MakotoKurauchi/helix/PCB/beta/helix.sch

## KiCad design PCB/beta/helix.sch (2018-01-27)

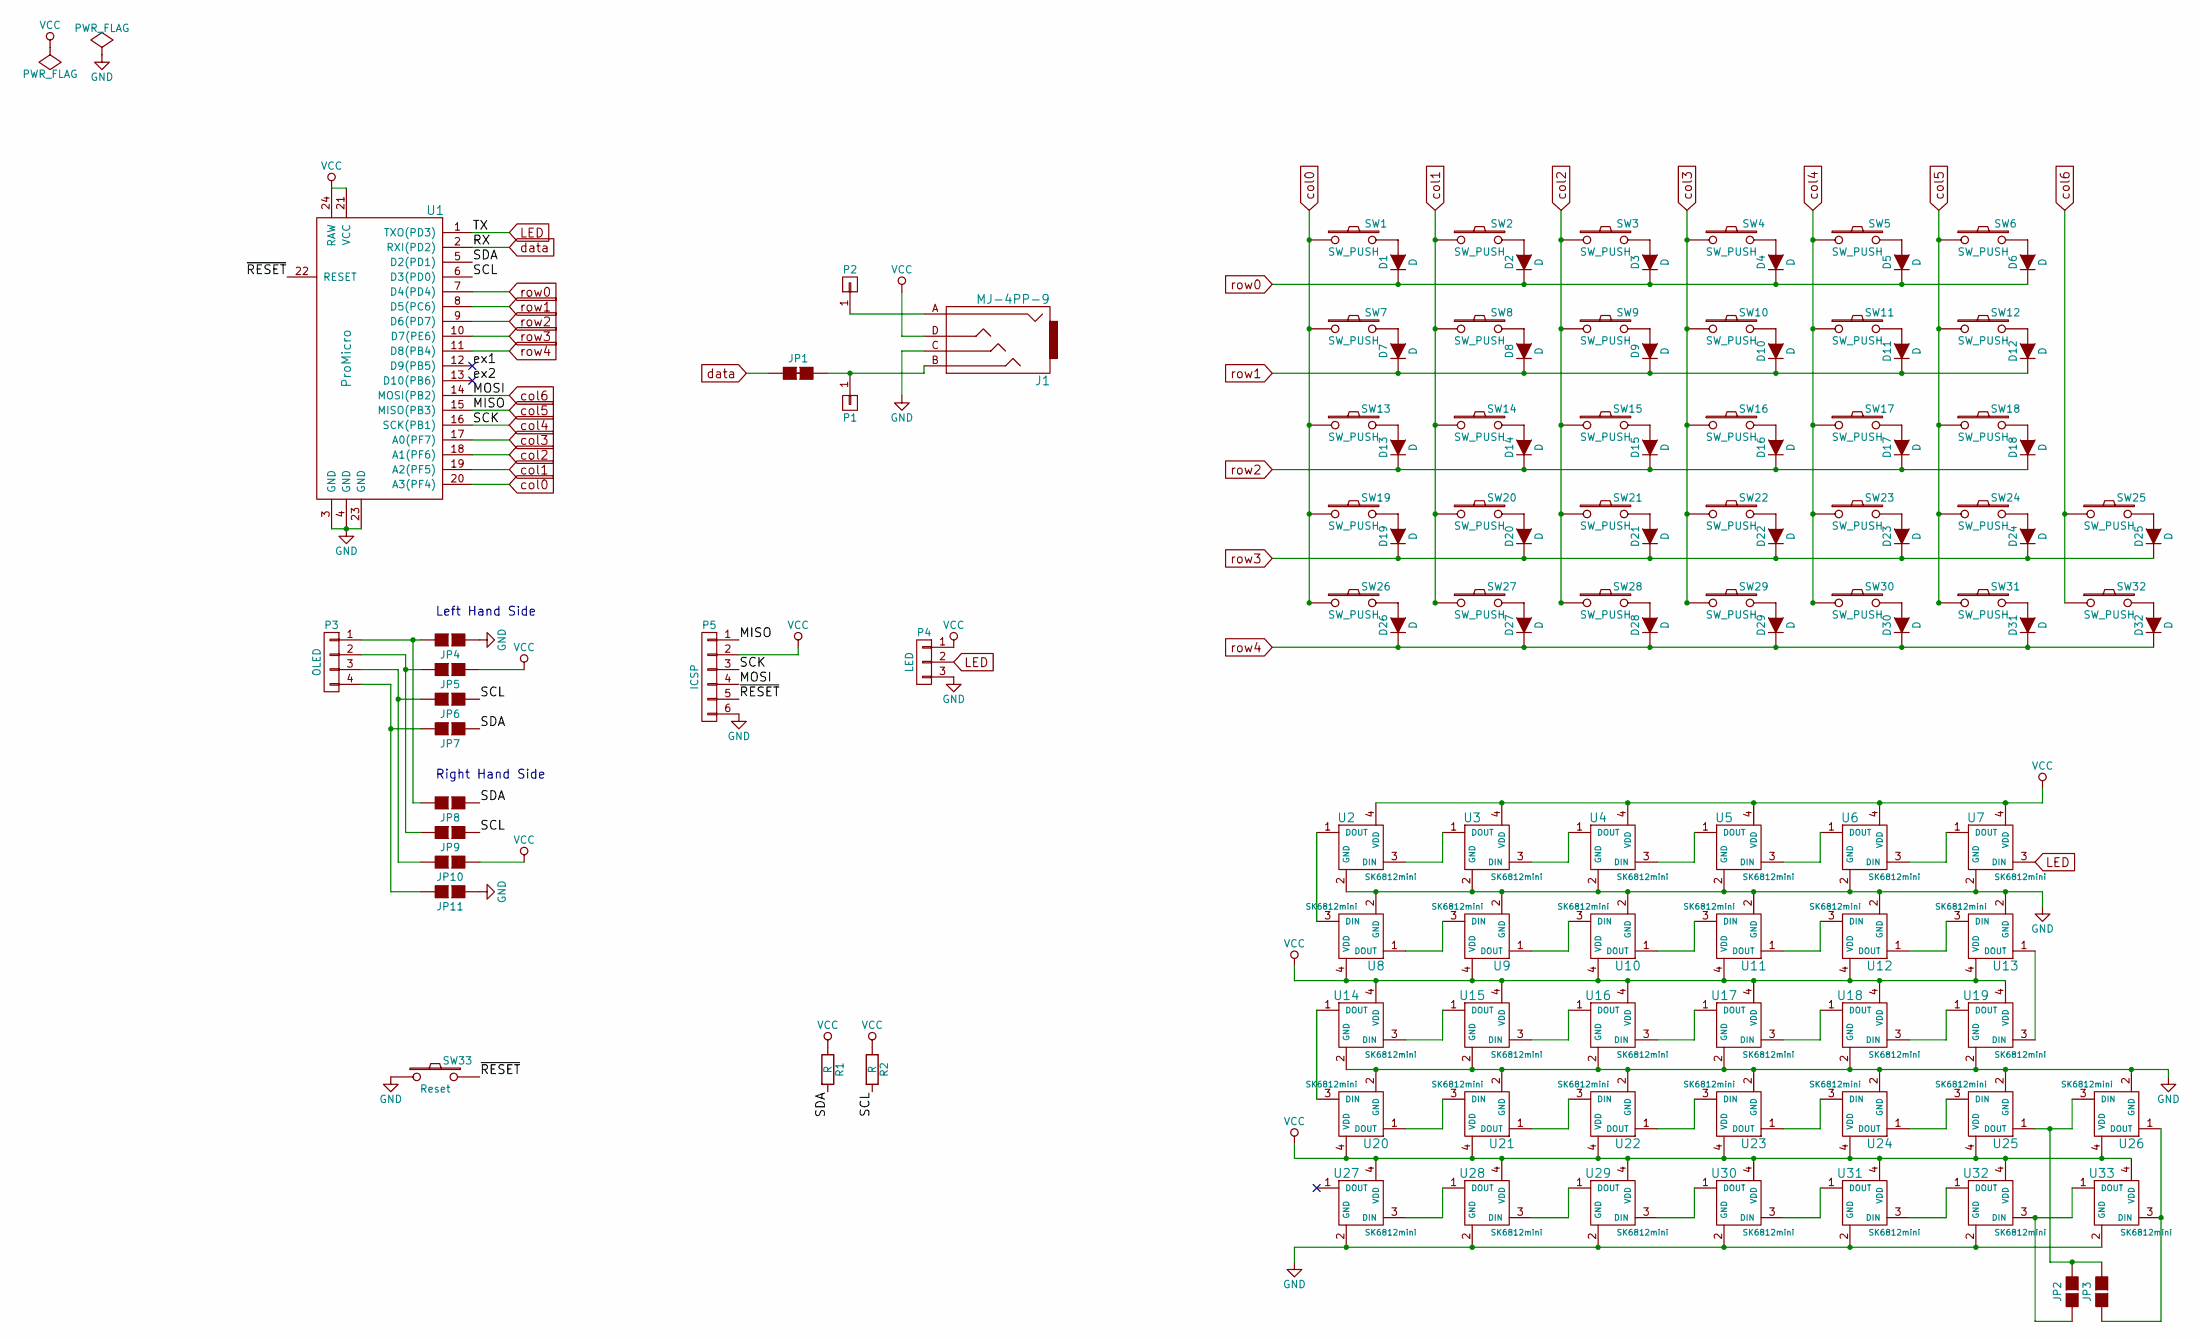
[picture p5: schematic helix.sch]

Parts:
D1, D2, D3, D4, D5, D6, D7, D8, D9, D10, D11, D12, D13, D14, D15, D16, D17, D18, D19, D20, D21, D22, D23, D24, D25, D26, D27, D28, D29, D30, D31, D32: D; D3_TH_SMD
J1: MJ-4PP-9; MJ-4PP-9_rev2
JP1: JPC2
JP2, JP3: JP2; Jumper
JP4, JP11: GND; Jumper
JP5, JP10: VCC; Jumper
JP6, JP9: SCL; Jumper
JP7, JP8: SDA; Jumper
P1, P2: CONN_01X01; 1PIN_0.1
P3: OLED; MY_SIL-4
P4: LED; StripLED_rev
P5: ICSP; MY_SIL-2x3
R1, R2: R; R2
SW1, SW2, SW3, SW4, SW5, SW6, SW7, SW8, SW9, SW10, SW11, SW12, SW13, SW14, SW15, SW16, SW17, SW18, SW19, SW20, SW21, SW22, SW23, SW24, SW25, SW26, SW27, SW28, SW29, SW30, SW31, SW32: SW_PUSH; MX_ALPS_PG1350_noLed
SW33: Reset; SW_3.5x6.0_TH
U1: ProMicro; ProMicro_rev
U2, U3, U4, U5, U6, U7, U8, U9, U10, U11, U12, U13, U14, U15, U16, U17, U18, U19, U20, U21, U22, U23, U24, U25, U26, U27, U28, U29, U30, U31, U32, U33: SK6812mini; SK6812MINI_rev

Connections:
GND: J1.C, JP4.1 (G1), JP11.1 (G1), P4.3, P5.6, SW33.1, U1.3 (GND), U1.4 (GND), U1.23 (GND), U2.2 (GND), U3.2 (GND), U4.2 (GND), U5.2 (GND), U6.2 (GND), U7.2 (GND), U8.2 (GND), U9.2 (GND), U10.2 (GND), U11.2 (GND), U12.2 (GND), U13.2 (GND), U14.2 (GND), U15.2 (GND), U16.2 (GND), U17.2 (GND), U18.2 (GND), U19.2 (GND), U20.2 (GND), U21.2 (GND), U22.2 (GND), U23.2 (GND), U24.2 (GND), U25.2 (GND), U26.2 (GND), U27.2 (GND), U28.2 (GND), U29.2 (GND), U30.2 (GND), U31.2 (GND), U32.2 (GND), U33.2 (GND)
LED: P4.2, U1.1 (TXO(PD3)), U7.3 (DIN)
unnamed: D1.2 (A), SW1.2
unnamed: D2.2 (A), SW2.2
unnamed: D3.2 (A), SW3.2
unnamed: D4.2 (A), SW4.2
unnamed: D5.2 (A), SW5.2
unnamed: D6.2 (A), SW6.2
unnamed: D7.2 (A), SW7.2
unnamed: D8.2 (A), SW8.2
unnamed: D9.2 (A), SW9.2
unnamed: D10.2 (A), SW10.2
unnamed: D11.2 (A), SW11.2
unnamed: D12.2 (A), SW12.2
unnamed: D13.2 (A), SW13.2
unnamed: D14.2 (A), SW14.2
unnamed: D15.2 (A), SW15.2
unnamed: D16.2 (A), SW16.2
unnamed: D17.2 (A), SW17.2
unnamed: D18.2 (A), SW18.2
unnamed: D19.2 (A), SW19.2
unnamed: D20.2 (A), SW20.2
unnamed: D21.2 (A), SW21.2
unnamed: D22.2 (A), SW22.2
unnamed: D23.2 (A), SW23.2
unnamed: D24.2 (A), SW24.2
unnamed: D25.2 (A), SW25.2
unnamed: D26.2 (A), SW26.2
unnamed: D27.2 (A), SW27.2
unnamed: D28.2 (A), SW28.2
unnamed: D29.2 (A), SW29.2
unnamed: D30.2 (A), SW30.2
unnamed: D31.2 (A), SW31.2
unnamed: D32.2 (A), SW32.2
unnamed: J1.A, P2.1
unnamed: J1.B, JP1.2 (G2), P1.1
unnamed: JP2.1 (G1), U32.3 (DIN), U33.1 (DOUT)
unnamed: JP2.2 (G2), JP3.2 (G2), U25.1 (DOUT), U26.3 (DIN)
unnamed: JP3.1 (G1), U26.1 (DOUT), U33.3 (DIN)
unnamed: JP4.2 (G2), JP8.2 (G2), P3.1
unnamed: JP5.2 (G2), JP9.2 (G2), P3.2
unnamed: JP6.2 (G2), JP10.2 (G2), P3.3
unnamed: JP7.2 (G2), JP11.2 (G2), P3.4
unnamed: U2.1 (DOUT), U8.3 (DIN)
unnamed: U2.3 (DIN), U3.1 (DOUT)
unnamed: U3.3 (DIN), U4.1 (DOUT)
unnamed: U4.3 (DIN), U5.1 (DOUT)
unnamed: U5.3 (DIN), U6.1 (DOUT)
unnamed: U6.3 (DIN), U7.1 (DOUT)
unnamed: U8.1 (DOUT), U9.3 (DIN)
unnamed: U10.1 (DOUT), U11.3 (DIN)
unnamed: U9.1 (DOUT), U10.3 (DIN)
unnamed: U11.1 (DOUT), U12.3 (DIN)
unnamed: U12.1 (DOUT), U13.3 (DIN)
unnamed: U13.1 (DOUT), U19.3 (DIN)
unnamed: U14.1 (DOUT), U20.3 (DIN)
unnamed: U14.3 (DIN), U15.1 (DOUT)
unnamed: U15.3 (DIN), U16.1 (DOUT)
unnamed: U16.3 (DIN), U17.1 (DOUT)
unnamed: U17.3 (DIN), U18.1 (DOUT)
unnamed: U18.3 (DIN), U19.1 (DOUT)
unnamed: U20.1 (DOUT), U21.3 (DIN)
unnamed: U21.1 (DOUT), U22.3 (DIN)
unnamed: U22.1 (DOUT), U23.3 (DIN)
unnamed: U23.1 (DOUT), U24.3 (DIN)
unnamed: U24.1 (DOUT), U25.3 (DIN)
unnamed: U27.3 (DIN), U28.1 (DOUT)
unnamed: U28.3 (DIN), U29.1 (DOUT)
unnamed: U29.3 (DIN), U30.1 (DOUT)
unnamed: U30.3 (DIN), U31.1 (DOUT)
unnamed: U31.3 (DIN), U32.1 (DOUT)
SCL: JP6.1 (G1), JP9.1 (G1), R2.2, U1.6 (D3(PD0))
SDA: JP7.1 (G1), JP8.1 (G1), R1.2, U1.5 (D2(PD1))
VCC: J1.D, JP5.1 (G1), JP10.1 (G1), P4.1, P5.2, R1.1, R2.1, U1.21 (VCC), U1.24 (RAW), U2.4 (VDD), U3.4 (VDD), U4.4 (VDD), U5.4 (VDD), U6.4 (VDD), U7.4 (VDD), U8.4 (VDD), U9.4 (VDD), U10.4 (VDD), U11.4 (VDD), U12.4 (VDD), U13.4 (VDD), U14.4 (VDD), U15.4 (VDD), U16.4 (VDD), U17.4 (VDD), U18.4 (VDD), U19.4 (VDD), U20.4 (VDD), U21.4 (VDD), U22.4 (VDD), U23.4 (VDD), U24.4 (VDD), U25.4 (VDD), U26.4 (VDD), U27.4 (VDD), U28.4 (VDD), U29.4 (VDD), U30.4 (VDD), U31.4 (VDD), U32.4 (VDD), U33.4 (VDD)
col0: SW1.1, SW7.1, SW13.1, SW19.1, SW26.1, U1.20 (A3(PF4))
col1: SW2.1, SW8.1, SW14.1, SW20.1, SW27.1, U1.19 (A2(PF5))
col2: SW3.1, SW9.1, SW15.1, SW21.1, SW28.1, U1.18 (A1(PF6))
col3: SW4.1, SW10.1, SW16.1, SW22.1, SW29.1, U1.17 (A0(PF7))
col4: P5.3, SW5.1, SW11.1, SW17.1, SW23.1, SW30.1, U1.16 (SCK(PB1))
col5: P5.1, SW6.1, SW12.1, SW18.1, SW24.1, SW31.1, U1.15 (MISO(PB3))
col6: P5.4, SW25.1, SW32.1, U1.14 (MOSI(PB2))
data: JP1.1 (G1), U1.2 (RXI(PD2))
ex1: U1.12 (D9(PB5))
ex2: U1.13 (D10(PB6))
row0: D1.1 (K), D2.1 (K), D3.1 (K), D4.1 (K), D5.1 (K), D6.1 (K), U1.7 (D4(PD4))
row1: D7.1 (K), D8.1 (K), D9.1 (K), D10.1 (K), D11.1 (K), D12.1 (K), U1.8 (D5(PC6))
row2: D13.1 (K), D14.1 (K), D15.1 (K), D16.1 (K), D17.1 (K), D18.1 (K), U1.9 (D6(PD7))
row3: D19.1 (K), D20.1 (K), D21.1 (K), D22.1 (K), D23.1 (K), D24.1 (K), D25.1 (K), U1.10 (D7(PE6))
row4: D26.1 (K), D27.1 (K), D28.1 (K), D29.1 (K), D30.1 (K), D31.1 (K), D32.1 (K), U1.11 (D8(PB4))
~RESET: P5.5, SW33.2, U1.22 (RESET)

Notes on the sheet:
Left Hand Side
Right Hand Side
